BustosJorge/Dragonfly/Models 3D/Type_C_Female_Connector/Type_c_connector.png

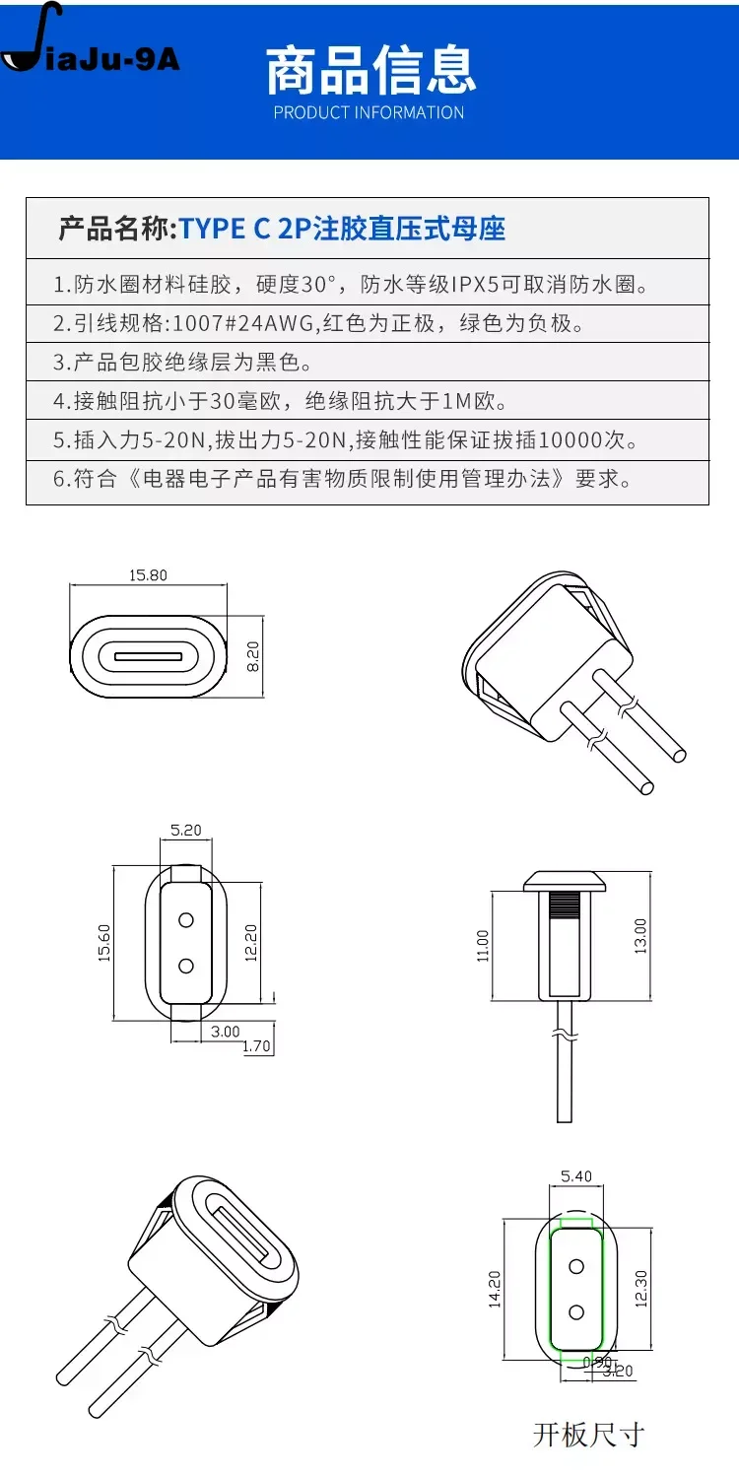
Models 3D/Type_C_Female_Connector/Type_c_connector.png
