BustosJorge/Dragonfly/Models 3D/Cap/Cap.SLDPRT

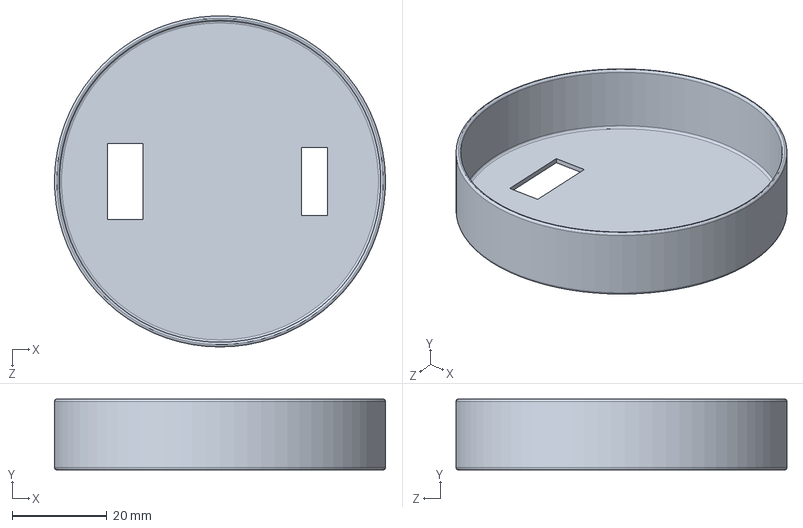
[picture p14: CAD file, 2024-07-02]
Models 3D/Cap/Cap.SLDPRT
70.0 x 15.0 x 70.0 mm
