BustosJorge/Dragonfly/Models 3D/Jar/Jar.SLDPRT

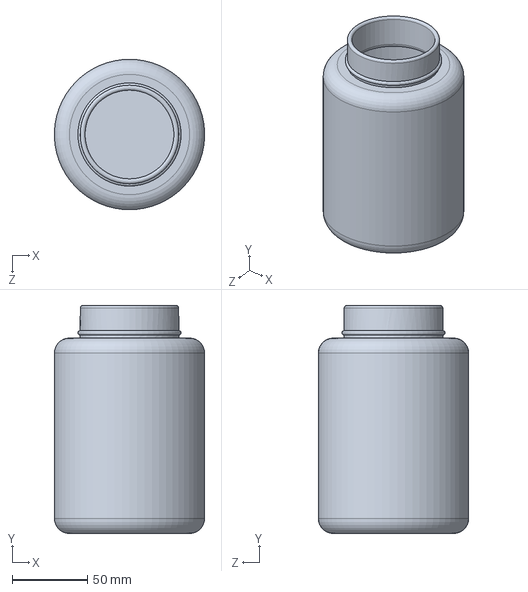
[picture p15: CAD file, 2024-07-02]
Models 3D/Jar/Jar.SLDPRT
99.9 x 151.6 x 100.0 mm
