BustosJorge/Dragonfly/Models 3D/Soporte_base/Soporte_base.SLDPRT

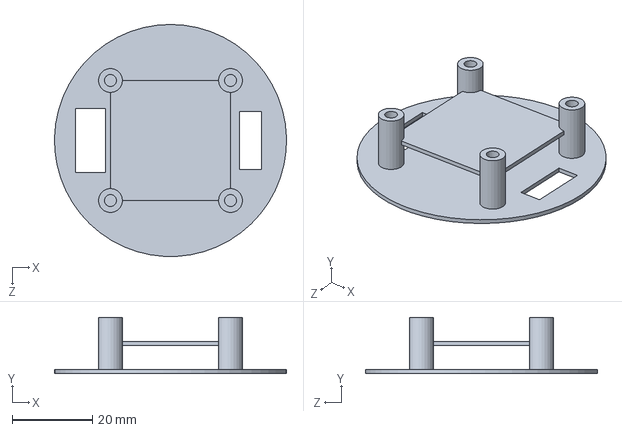
[picture p16: CAD file, 2024-07-02]
Models 3D/Soporte_base/Soporte_base.SLDPRT
58.0 x 14.0 x 58.0 mm
