BustosJorge/Dragonfly/Models 3D/SW_2P2T/SW_2P2T.SLDPRT

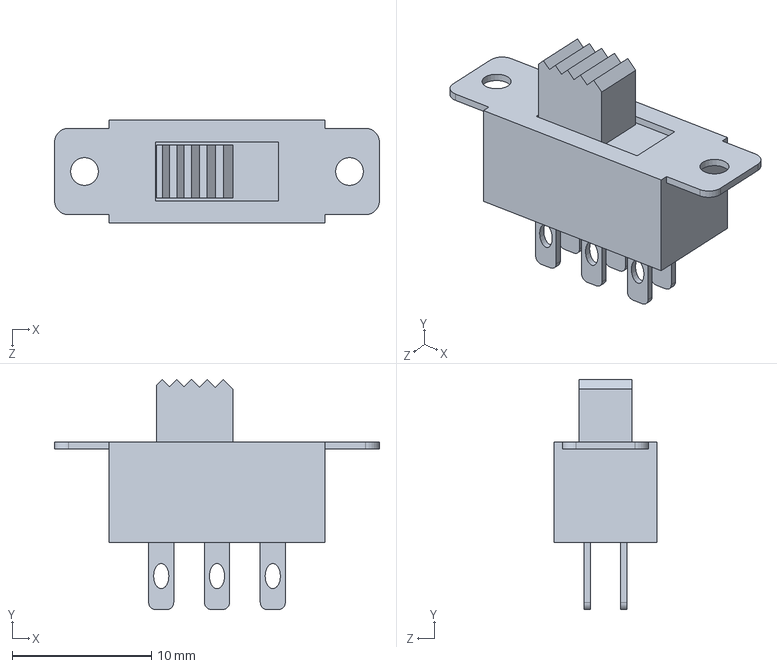
[picture p17: CAD file, 2024-07-02]
Models 3D/SW_2P2T/SW_2P2T.SLDPRT
23.3 x 16.5 x 7.40 mm
