BustosJorge/Dragonfly/Models 3D/Type_C_Female_Connector/Type_C_Female_Connector.SLDPRT

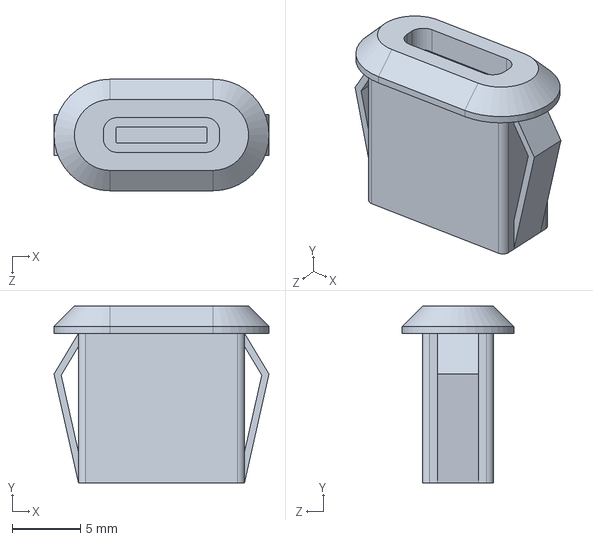
[picture p18: CAD file, 2024-07-02]
Models 3D/Type_C_Female_Connector/Type_C_Female_Connector.SLDPRT
15.8 x 13.0 x 8.20 mm
