BustosJorge/Dragonfly/Models 3D/Ensamblaje/IMG_1.JPG

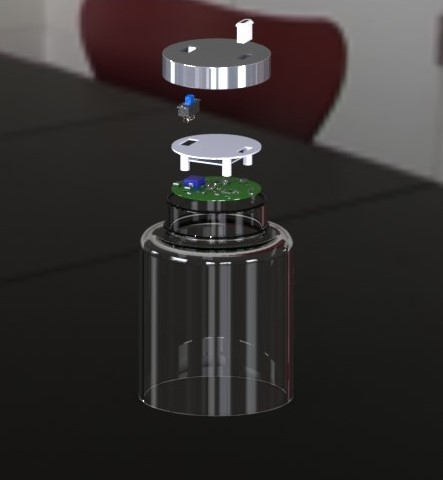
Models 3D/Ensamblaje/IMG_1.JPG
